jmjass/OpenOblong/PCB Files/OpenOblong/marbastlib/3d/SW_SKHLLC.step

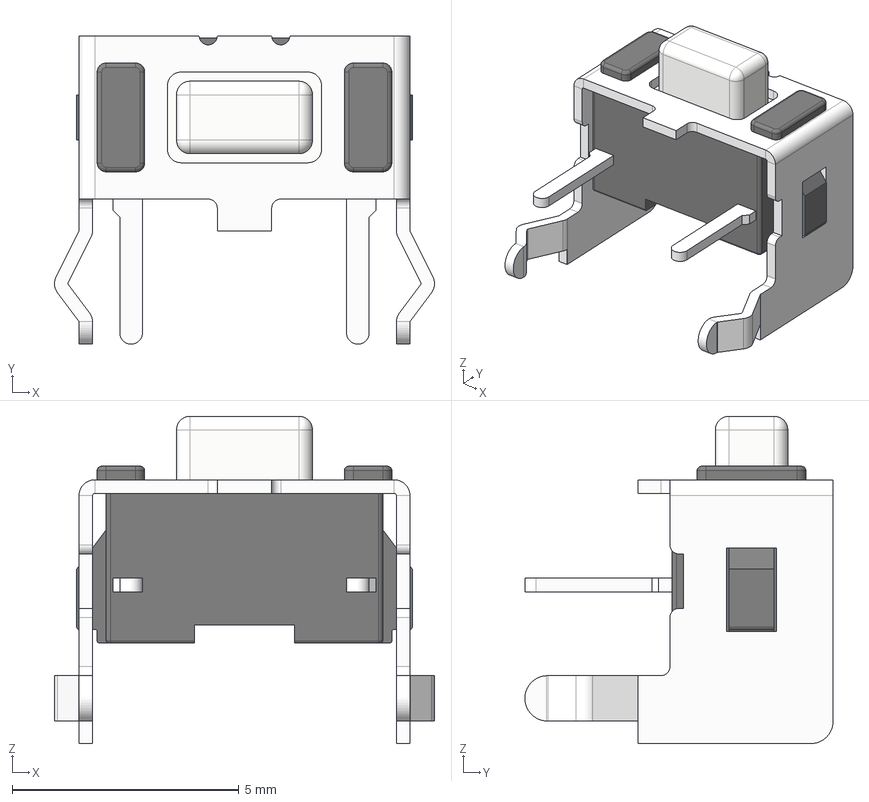
[picture p16: CAD file, 2023-07-22]
PCB Files/OpenOblong/marbastlib/3d/SW_SKHLLC.step
8.38 x 6.80 x 7.22 mm
