jmjass/OpenOblong/PCB Files/OpenOblongChocs/marbastlib/3d/Crystal_FA-128.step

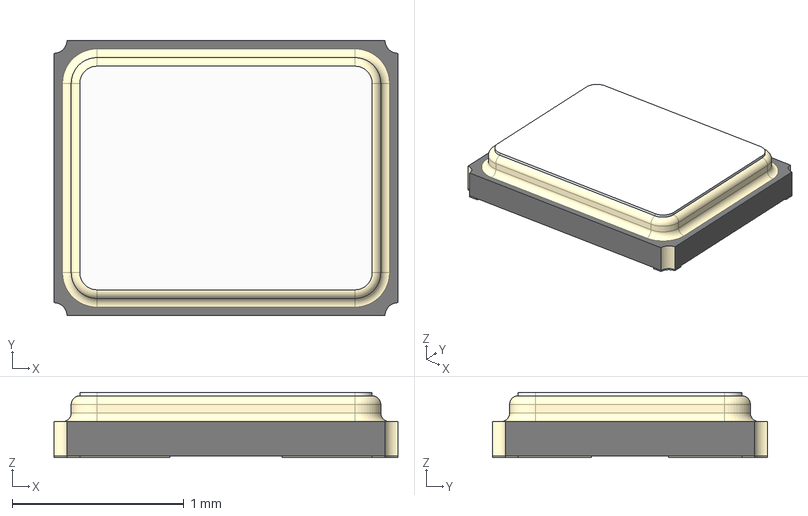
[picture p17: CAD file, 2023-07-22]
PCB Files/OpenOblongChocs/marbastlib/3d/Crystal_FA-128.step
2.00 x 1.60 x 0.38 mm
