jmjass/OpenOblong/CubsCase/BottomLayer.dxf

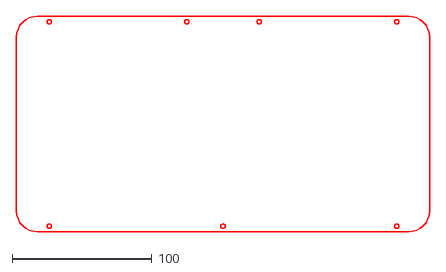
[picture p18: CAD file, 2023-05-22]
CubsCase/BottomLayer.dxf
296.0 x 154.4
