jmjass/OpenOblong/PCB Files/OpenOblong/marbastlib/3d/CON_SM08B-SRSS-TB.step

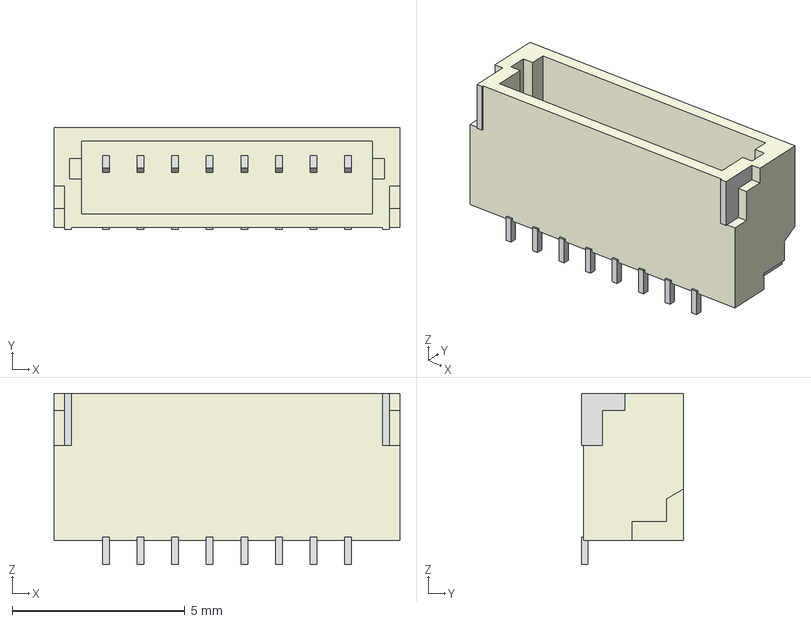
[picture p19: CAD file, 2023-07-22]
PCB Files/OpenOblong/marbastlib/3d/CON_SM08B-SRSS-TB.step
10.0 x 2.96 x 4.95 mm
