jmjass/OpenOblong/PCB Files/OpenOblongChocs/marbastlib/3d/PNT_psp1000.step

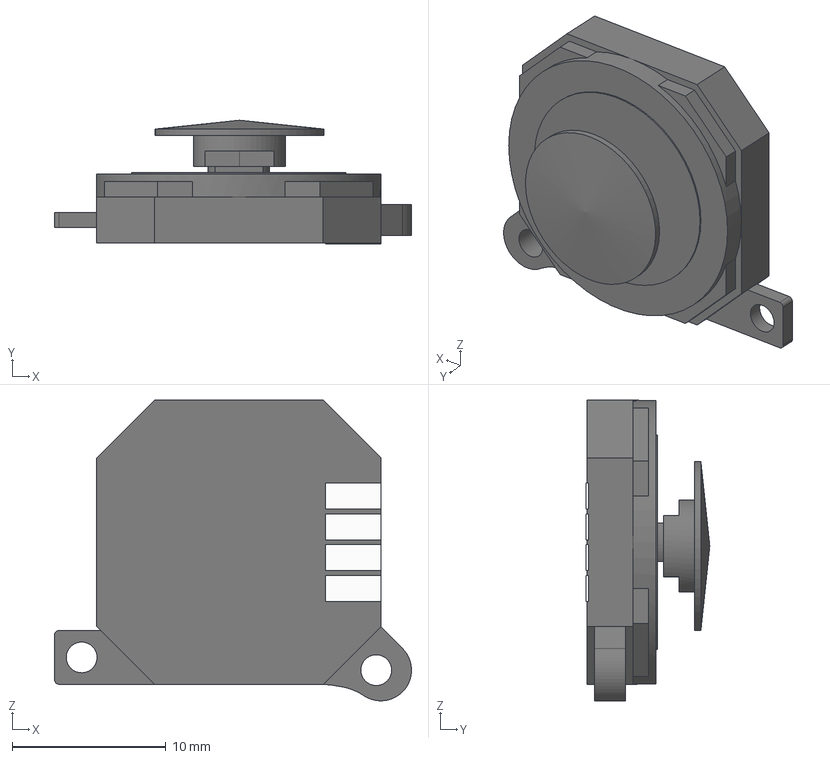
[picture p20: CAD file, 2023-07-22]
PCB Files/OpenOblongChocs/marbastlib/3d/PNT_psp1000.step
23.2 x 8.05 x 19.6 mm
