jmjass/OpenOblong/CubsCase/baseLayer.dxf

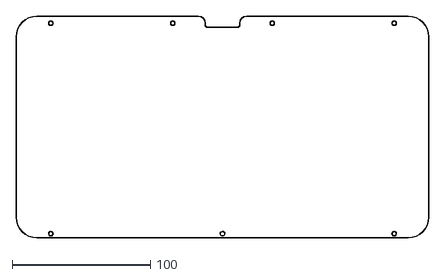
[picture p21: CAD file, 2023-03-18]
CubsCase/baseLayer.dxf
298.8 x 160.4
