jmjass/OpenOblong/PCB Files/OpenOblong/marbastlib/3d/MSK12C02.step

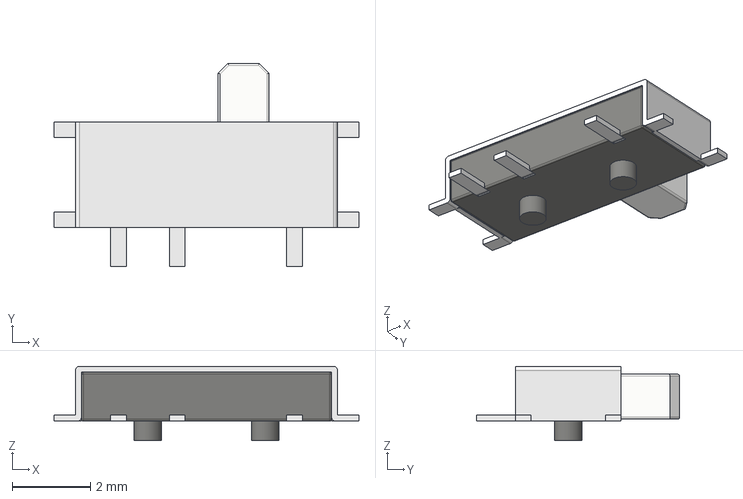
[picture p22: CAD file, 2023-07-22]
PCB Files/OpenOblong/marbastlib/3d/MSK12C02.step
7.80 x 5.20 x 1.90 mm
