jmjass/OpenOblong/PCB Files/OpenOblongChocs/marbastlib/3d/CON_SM07B-SRSS-TB.step

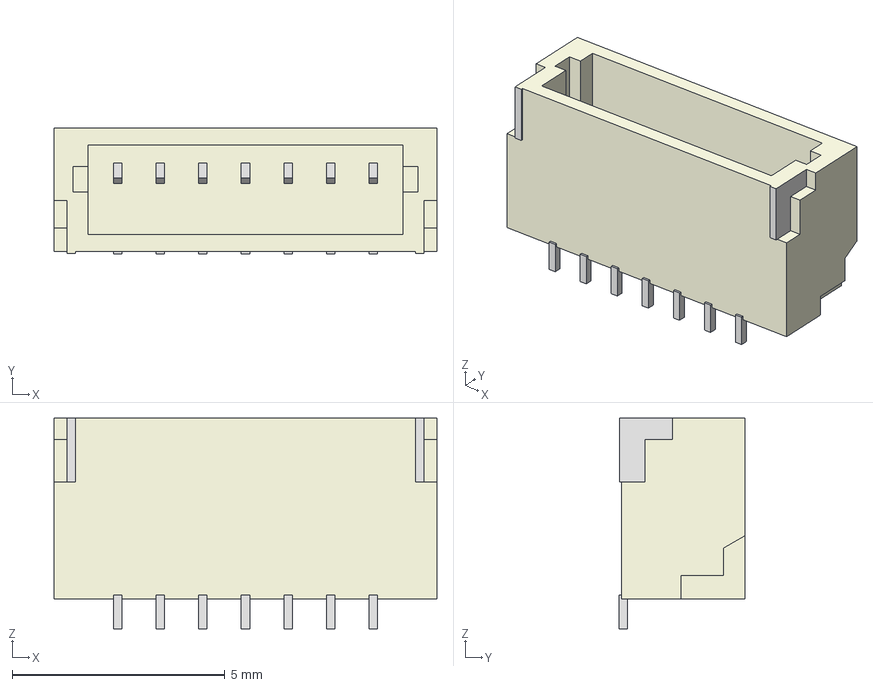
[picture p23: CAD file, 2023-07-22]
PCB Files/OpenOblongChocs/marbastlib/3d/CON_SM07B-SRSS-TB.step
9.00 x 2.96 x 4.95 mm
