jmjass/OpenOblong/PCB Files/OpenOblongChocs/marbastlib/3d/CON_MJ-4PP-9.step

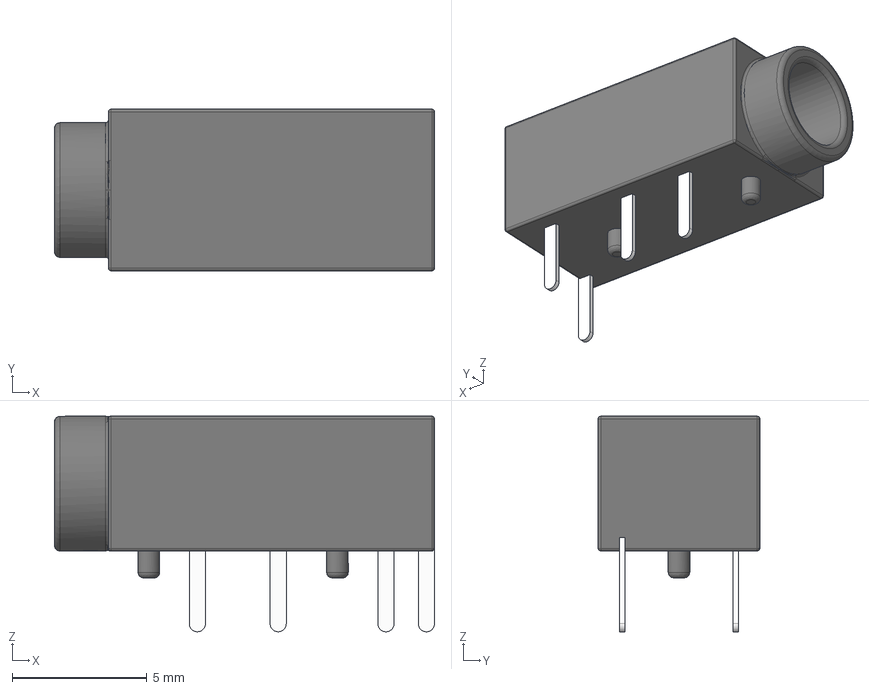
[picture p24: CAD file, 2023-07-22]
PCB Files/OpenOblongChocs/marbastlib/3d/CON_MJ-4PP-9.step
14.1 x 6.00 x 8.00 mm
