jmjass/OpenOblong/PCB Files/OpenOblong/marbastlib/3d/HS_Kailh_Choc.step

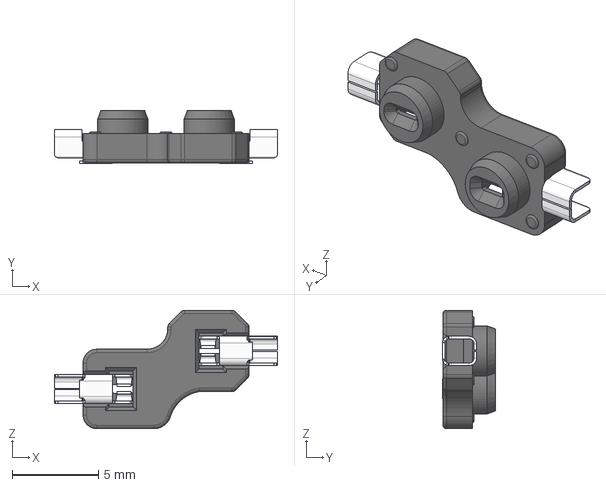
[picture p25: CAD file, 2023-07-22]
PCB Files/OpenOblong/marbastlib/3d/HS_Kailh_Choc.step
12.9 x 3.09 x 6.85 mm
pin x 2
socket
