jmjass/OpenOblong/PCB Files/OpenOblongChocs/marbastlib/3d/HS_Kailh_MX.step

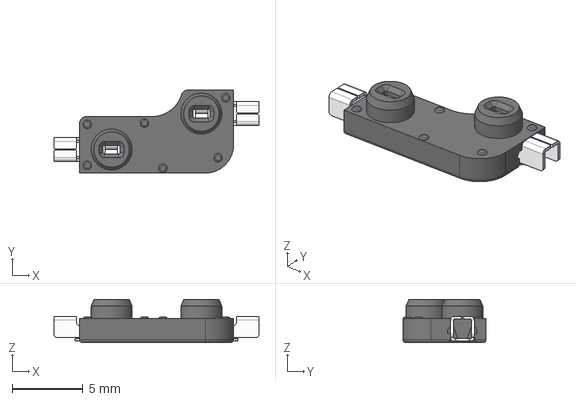
[picture p26: CAD file, 2023-07-22]
PCB Files/OpenOblongChocs/marbastlib/3d/HS_Kailh_MX.step
14.5 x 5.89 x 3.05 mm
Contact x 2
