jmjass/OpenOblong/PCB Files/OpenOblong/marbastlib/3d/SW_SSSS213100.step

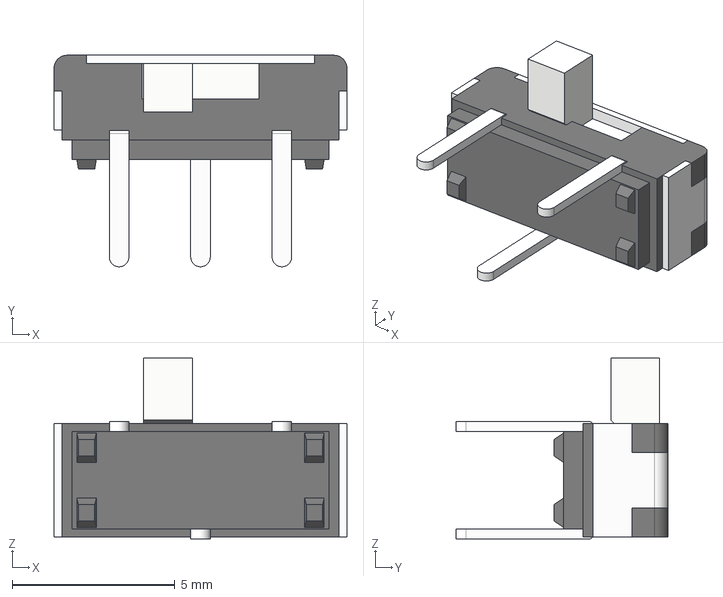
[picture p27: CAD file, 2023-07-22]
PCB Files/OpenOblong/marbastlib/3d/SW_SSSS213100.step
9.00 x 6.50 x 5.55 mm
