jmjass/OpenOblong/PCB Files/OpenOblong/marbastlib/3d/CON_TYPE-C-31-M-14.step

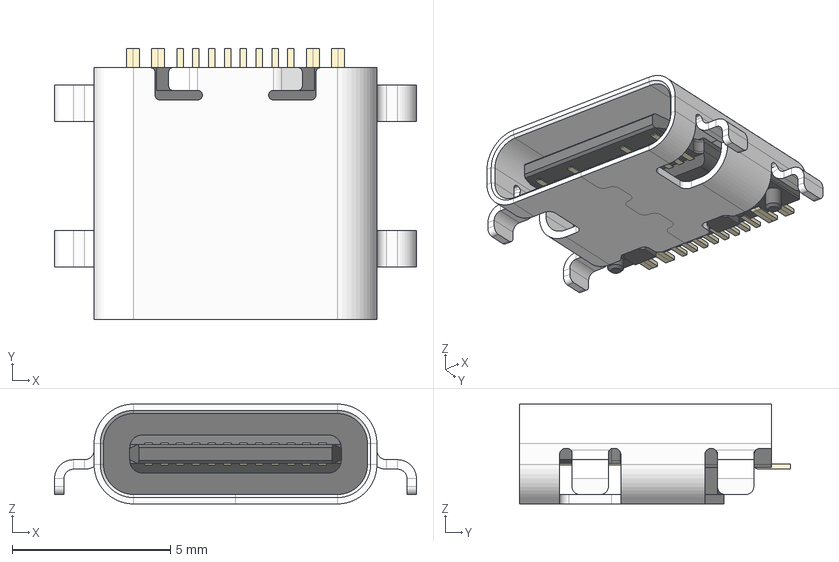
[picture p28: CAD file, 2023-07-22]
PCB Files/OpenOblong/marbastlib/3d/CON_TYPE-C-31-M-14.step
11.5 x 8.56 x 3.16 mm
Shroud
Plastic Body & Connector
