jmjass/OpenOblong/PCB Files/OpenOblong/marbastlib/3d/PNT_RKJXU1210006.step

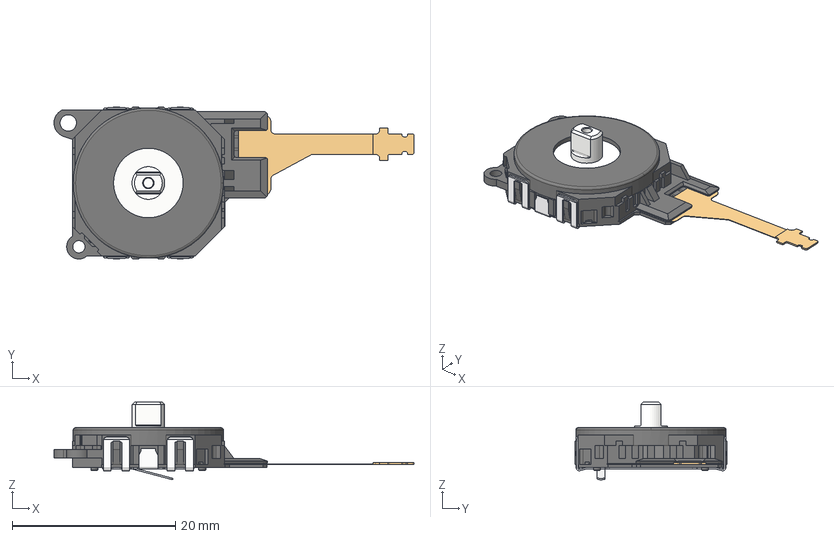
[picture p29: CAD file, 2023-07-22]
PCB Files/OpenOblong/marbastlib/3d/PNT_RKJXU1210006.step
44.0 x 18.6 x 9.50 mm
