jmjass/OpenOblong/PCB Files/OpenOblongChocs/marbastlib/3d/CON_TYPE-C-31-M-12.step

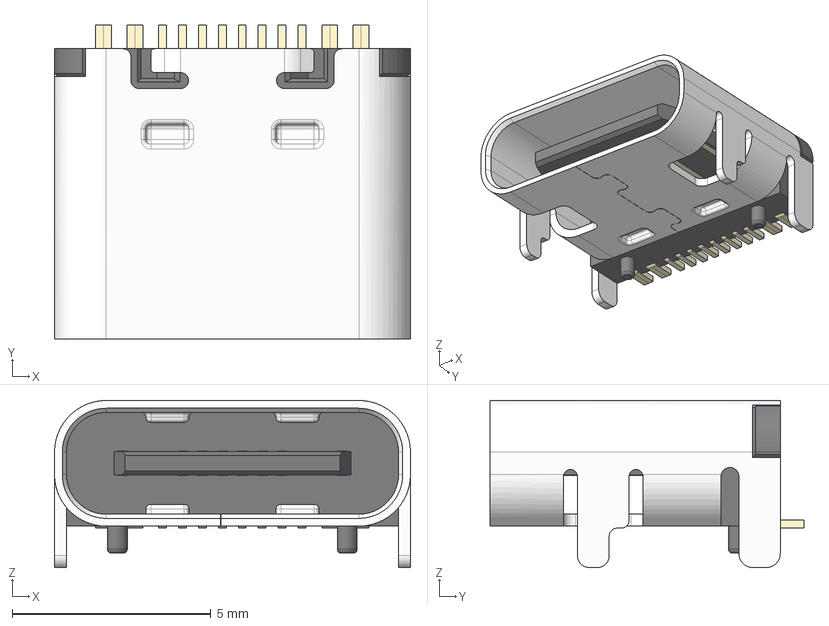
[picture p30: CAD file, 2023-07-22]
PCB Files/OpenOblongChocs/marbastlib/3d/CON_TYPE-C-31-M-12.step
8.95 x 7.90 x 4.20 mm
ConPins
PcbPins
Mold
Frame
