jmjass/OpenOblong/PCB Files/OpenOblong/marbastlib/3d/SW_SSSS223900.step

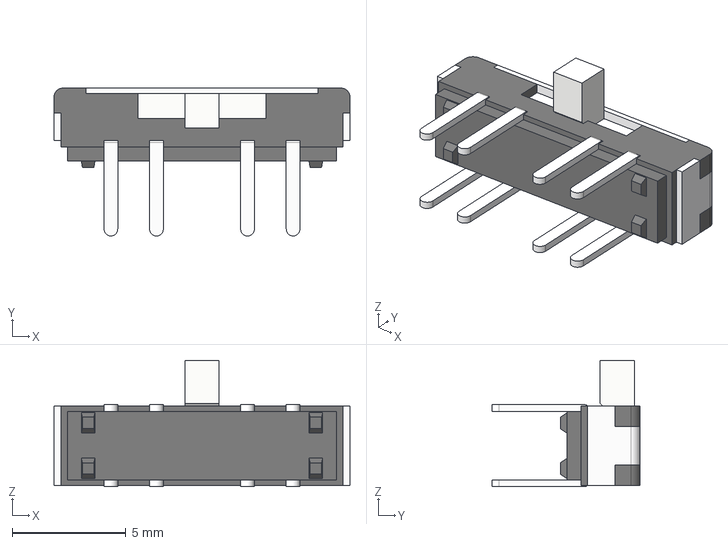
[picture p31: CAD file, 2023-07-22]
PCB Files/OpenOblong/marbastlib/3d/SW_SSSS223900.step
13.0 x 6.50 x 5.55 mm
