jmjass/OpenOblong/PCB Files/OpenOblong/marbastlib/3d/CON_BM02B-ACHSS.step

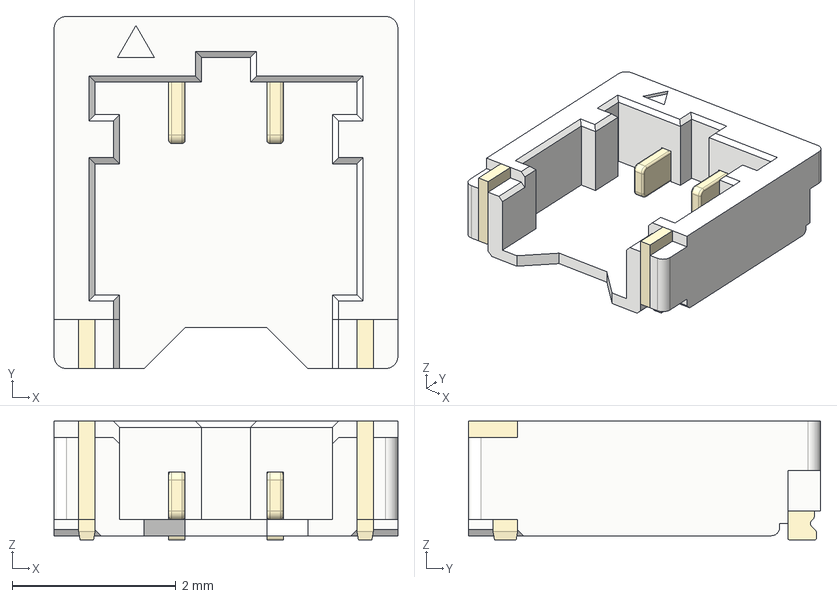
[picture p32: CAD file, 2023-07-22]
PCB Files/OpenOblong/marbastlib/3d/CON_BM02B-ACHSS.step
4.20 x 4.30 x 1.45 mm
