jmjass/OpenOblong/PCB Files/OpenOblongChocs/marbastlib/3d/ROT_EC11N.step

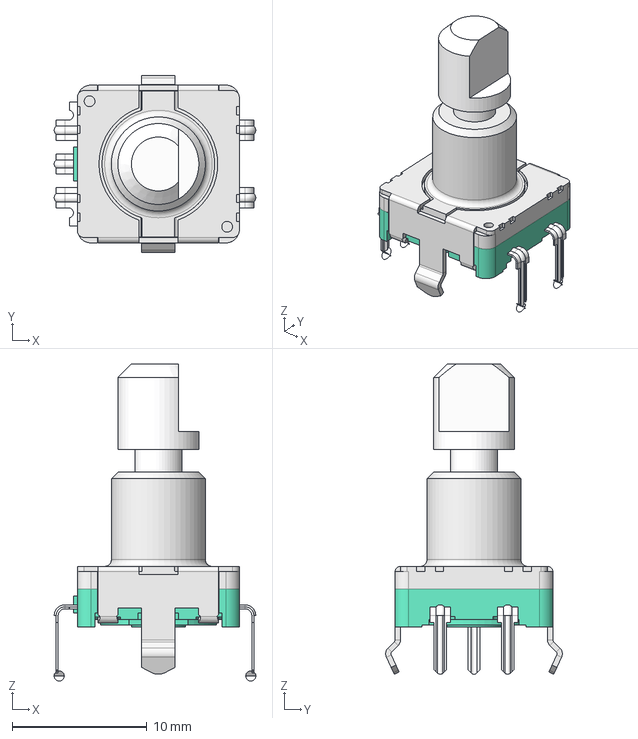
[picture p33: CAD file, 2023-07-22]
PCB Files/OpenOblongChocs/marbastlib/3d/ROT_EC11N.step
14.9 x 13.1 x 23.5 mm
