jmjass/OpenOblong/PCB Files/OpenOblongChocs/marbastlib/3d/CON_SM02B-SRSS-TB.step

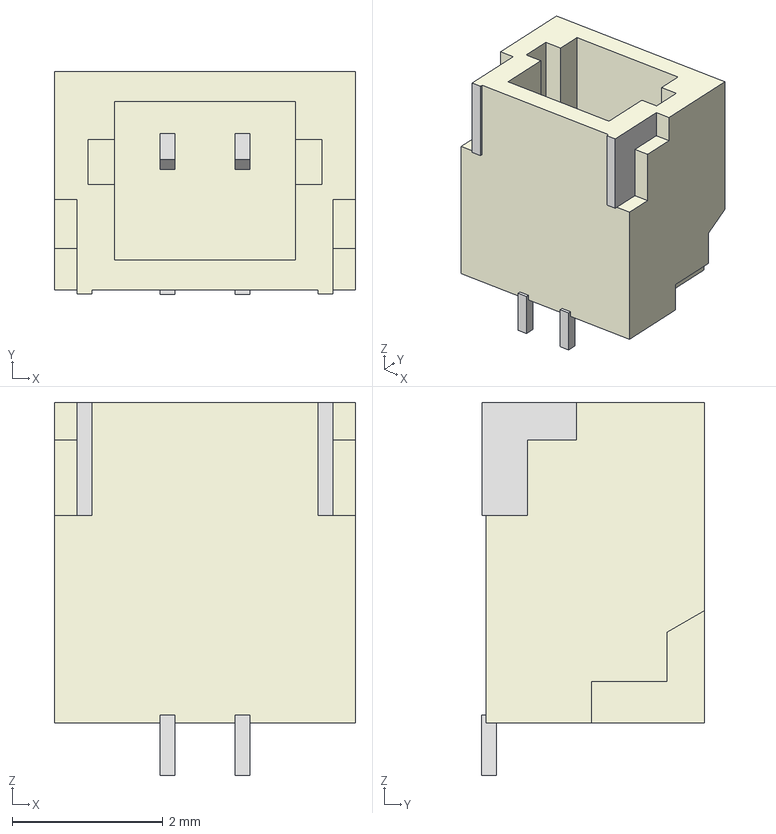
[picture p34: CAD file, 2023-07-22]
PCB Files/OpenOblongChocs/marbastlib/3d/CON_SM02B-SRSS-TB.step
4.00 x 2.96 x 4.95 mm
