jmjass/OpenOblong/PCB Files/OpenOblong/marbastlib/3d/CON_SM05B-SRSS-TB.step

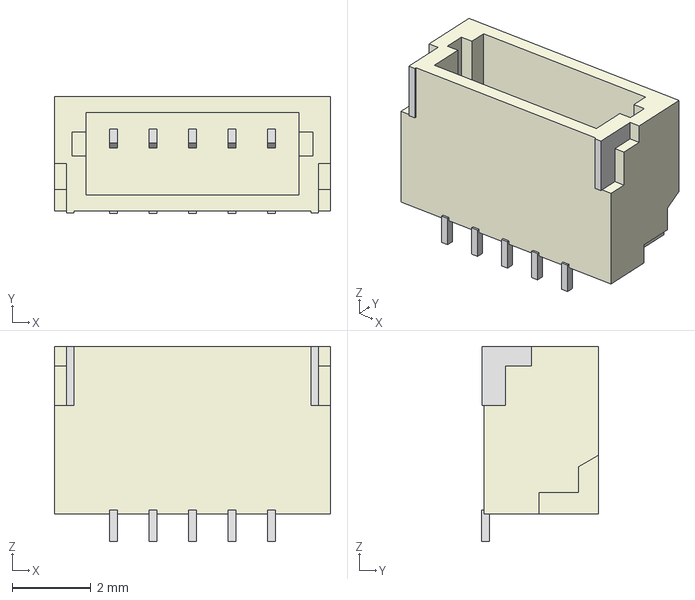
[picture p35: CAD file, 2023-07-22]
PCB Files/OpenOblong/marbastlib/3d/CON_SM05B-SRSS-TB.step
7.00 x 2.96 x 4.95 mm
