jmjass/OpenOblong/PCB Files/OpenOblong/marbastlib/3d/LED_SK6812MINI-E.step

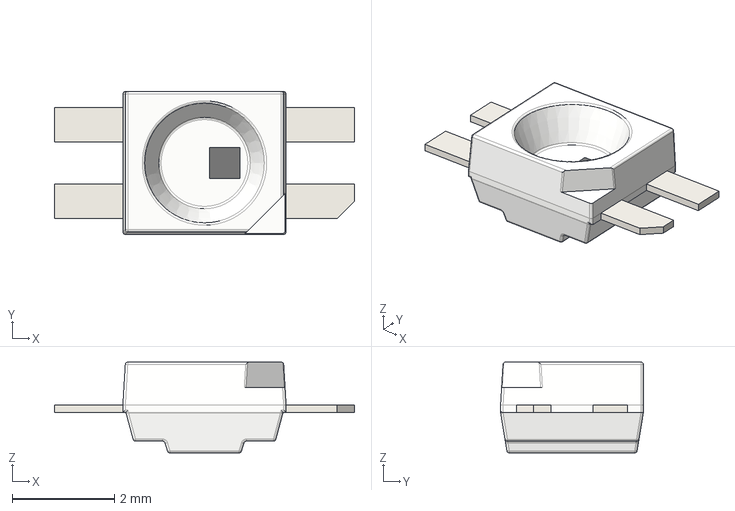
[picture p36: CAD file, 2023-07-22]
PCB Files/OpenOblong/marbastlib/3d/LED_SK6812MINI-E.step
5.88 x 2.80 x 1.78 mm
